TimBroeni/IM04_LNW/images/sortino_bildmarke.png

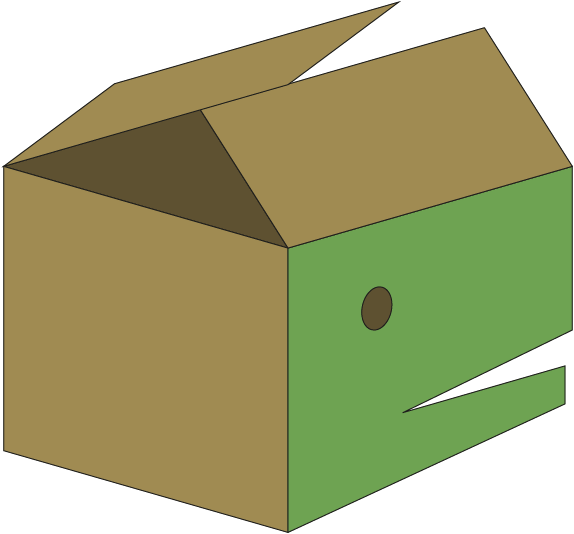
images/sortino_bildmarke.png
